simoninns/renault-twizy-speaker-mounts/images/20220502_124928.jpg

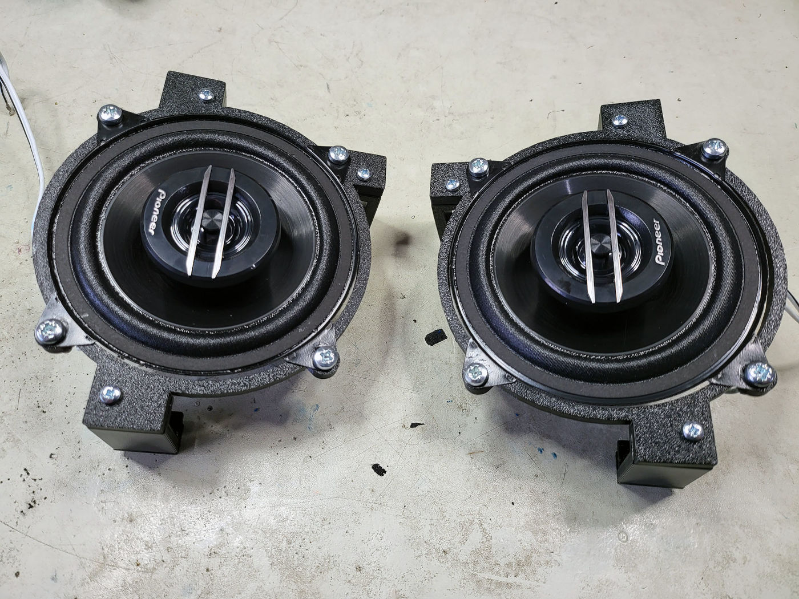
images/20220502_124928.jpg
