simoninns/renault-twizy-speaker-mounts/images/20220502_142655.jpg

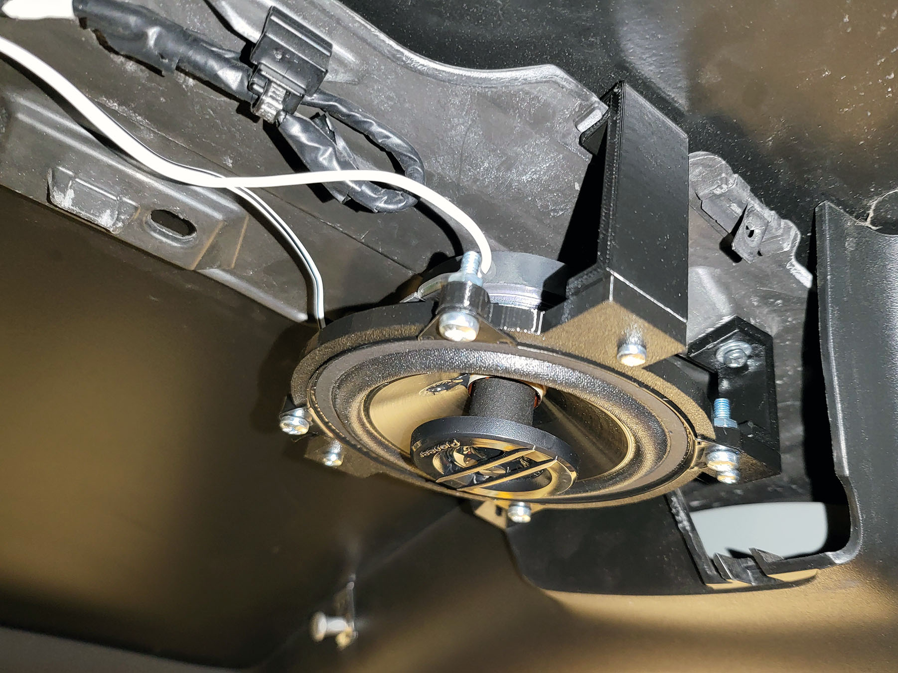
images/20220502_142655.jpg
