simoninns/renault-twizy-speaker-mounts/images/20220502_142724.jpg

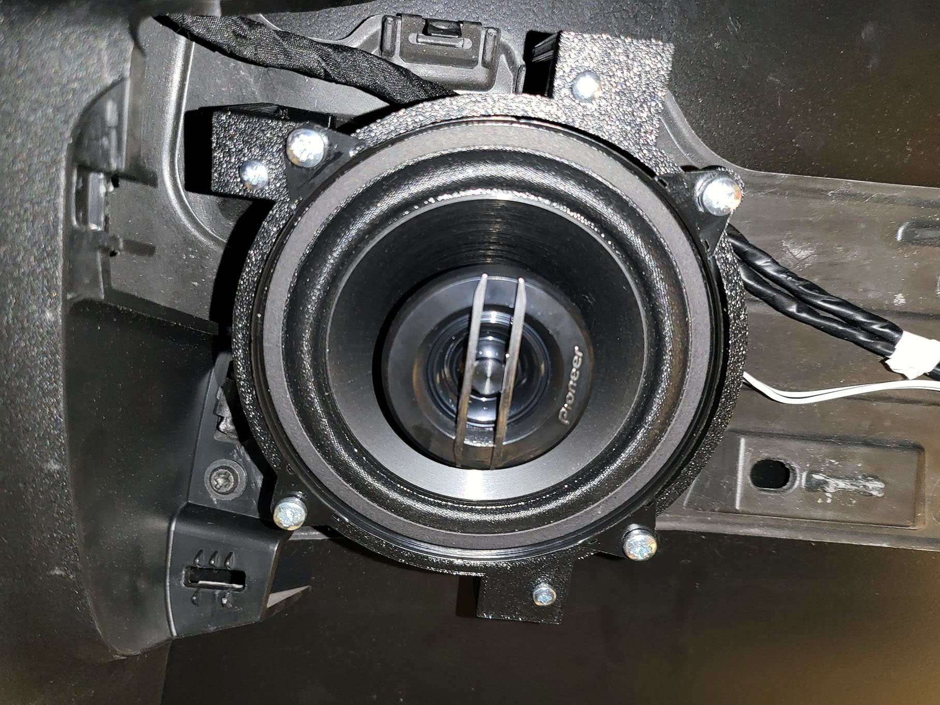
images/20220502_142724.jpg
